SomebodyYouMayKnow/cyberdeck/PCB/simple-power-mounting-template.pdf

# CYBERDECK / 1:1 MECHANICAL FIT TEMPLATE

### A4 landscape | TOP VIEW | all dimensions in mm | 2026-10-02

## FIT CHECK ONLY

### NOT FOR FABRICATION

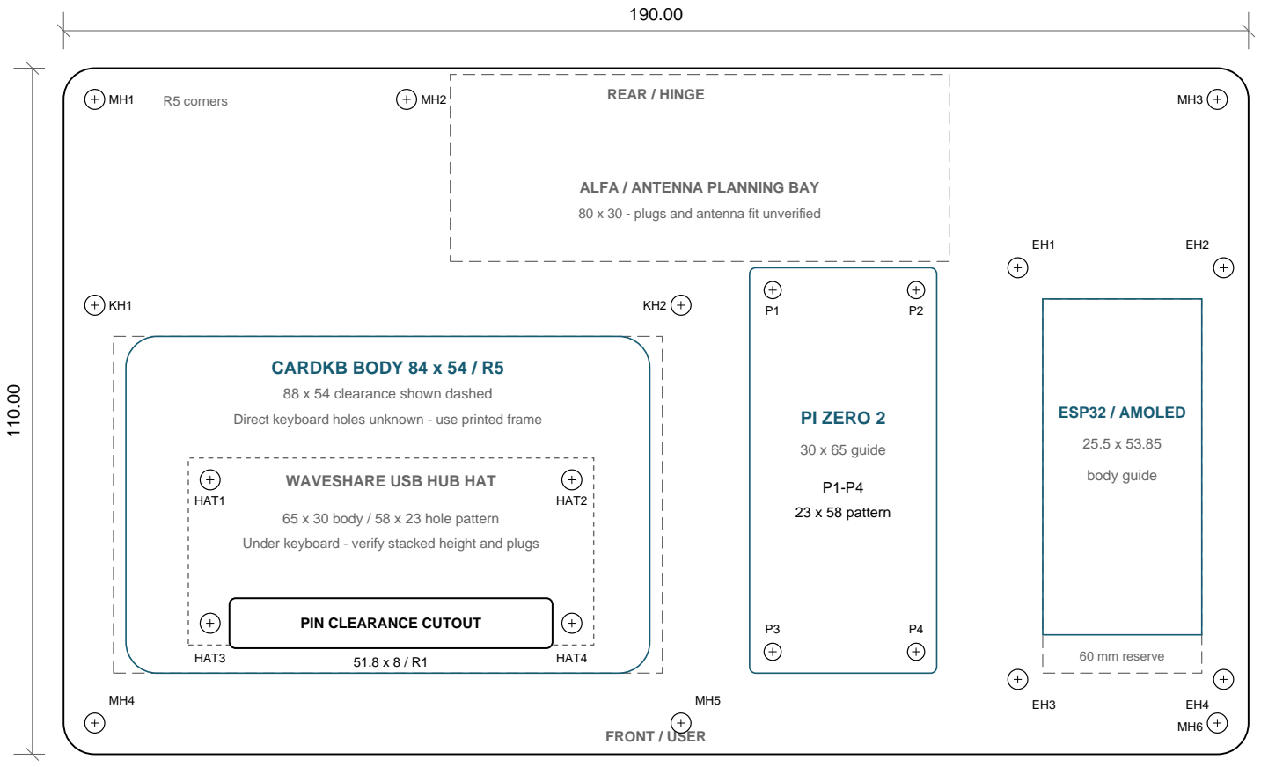
[picture p2: figure]
REAR / HINGE; FRONT / USER; R5 corners; CARDKB BODY 84 x 54 / R5; 88 x 54 clearance shown dashed; WAVESHARE USB HUB HAT; 65 x 30 body / 58 x 23 hole pattern; PIN CLEARANCE CUTOUT; PI ZERO 2; 30 x 65 guide; 23 x 58 pattern; ESP32 / AMOLED; body guide; 60 mm reserve; ALFA / ANTENNA PLANNING BAY; HAT1; HAT2; HAT3; HAT4

Direct keyboard holes unknown - use printed frame

Under keyboard - verify stacked height and plugs

80 x 30 - plugs and antenna fit unverified

## 20 CARRIER MOUNT HOLES

Datum: upper-left board extent; X right, Y down.
All NPTH; D = hole diameter. Solder holes omitted.
ID | X | Y | D
MH1 | 5.000 | 5.000 | 3.200
MH2 | 55.000 | 5.000 | 3.200
MH3 | 185.000 | 5.000 | 3.200
MH4 | 5.000 | 105.000 | 3.200
MH5 | 99.000 | 105.000 | 3.200
MH6 | 185.000 | 105.000 | 3.200
KH1 | 5.000 | 38.000 | 3.200
KH2 | 99.000 | 38.000 | 3.200
EH1 | 153.000 | 32.000 | 3.200
EH2 | 186.000 | 32.000 | 3.200
EH3 | 153.000 | 98.000 | 3.200
EH4 | 186.000 | 98.000 | 3.200
HAT1 | 23.500 | 66.000 | 3.200
HAT2 | 81.500 | 66.000 | 3.200
HAT3 | 23.500 | 89.000 | 3.200
HAT4 | 81.500 | 89.000 | 3.200
P1 | 113.698 | 35.579 | 2.750
P2 | 136.698 | 35.579 | 2.750
P3 | 113.698 | 93.579 | 2.750
P4 | 136.698 | 93.579 | 2.750

KH1, KH2, MH4, MH5: keyboard frame. EH1-EH4: ESP32 frame, not board holes. P1-P4: Pi mounting pads are NPTH.
No carrier power-module mounting holes.

Use insulating spacers / washers.
HAT3/4 head or spacer OD <=5.5 mm. External modules mount separately, insulated.

Planning outlines are not fit certification. Pi guide offset vs holes: ~0.20 / 0.08 mm. Check native hole centers against your Pi.

CardKB sources conflict: 84 or 88 mm wide. Measure the keyboard before printing its frame.

PRINT AT ACTUAL SIZE / 100% - disable Fit, Shrink and borderless expansion. Measure the calibration line before laying actual parts on the paper.

0 | 50 | 100 mm

Solid black: board edge / cutout / holes

Blue: component body planning guides

Dashed / dotted: clearance or raised HAT

Keyboard mounting holes are unknown. Four frame mounts are shown; do not drill the CardKB from this template.

Verify standoff heights, USB plugs, cable bends and Chameleon clearance with the real hardware.

Geometry: pcb-simple-power-native.json / 14c6ba430bfc | Outlines are planning guides; no copper or electrical validation.
